thingSoC/TSOC_GROVEY_UART/TSOC_GROVEY_UART/images/TSOC_GROVEY_UART_iso.png

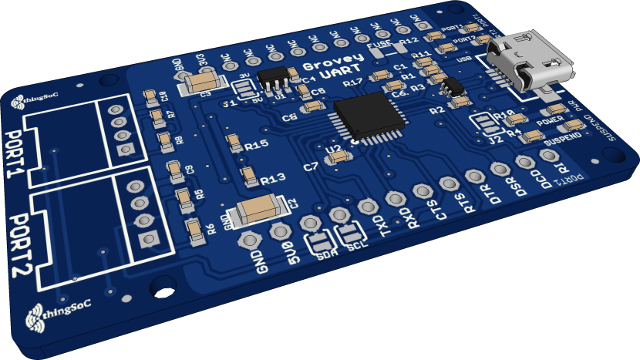
TSOC_GROVEY_UART/images/TSOC_GROVEY_UART_iso.png
